GaryFDes/IIgs-rthab/pictures/Bottom of Board.jpeg

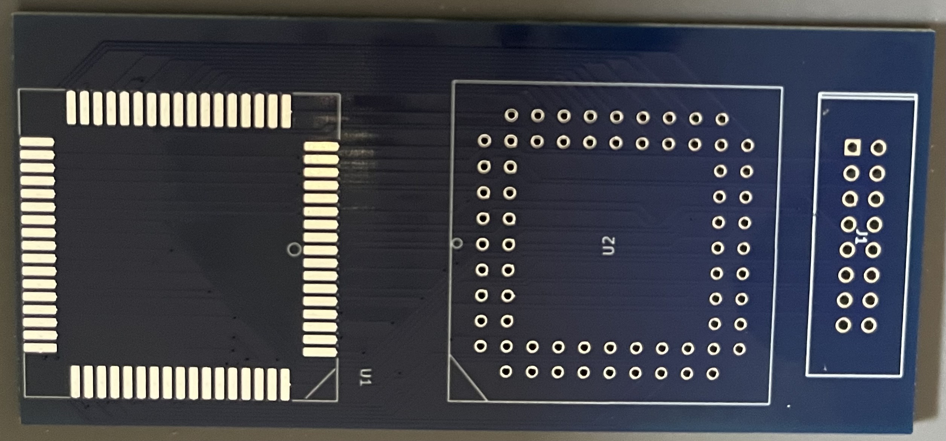
pictures/Bottom of Board.jpeg
